juergenpabel/HAL9000/enclosure/services/dashboard/resources/images/ATM.jpg

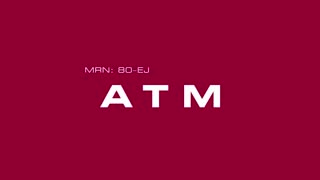
enclosure/services/dashboard/resources/images/ATM.jpg
