juergenpabel/HAL9000/enclosure/services/dashboard/resources/images/CNT.jpg

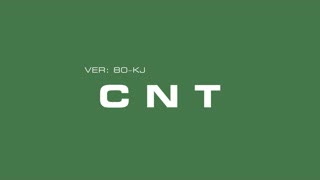
enclosure/services/dashboard/resources/images/CNT.jpg
