juergenpabel/HAL9000/enclosure/services/dashboard/resources/images/FLX.jpg

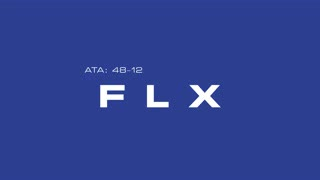
enclosure/services/dashboard/resources/images/FLX.jpg
