juergenpabel/HAL9000/enclosure/services/frontend/resources/images/animations/hal9000/fade-in/01.jpg

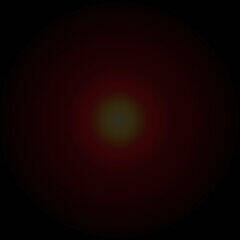
enclosure/services/frontend/resources/images/animations/hal9000/fade-in/01.jpg
