juergenpabel/HAL9000/enclosure/services/frontend/resources/images/animations/hal9000/fade-in/02.jpg

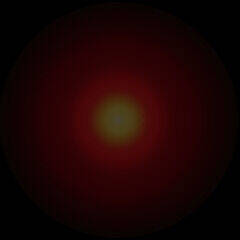
enclosure/services/frontend/resources/images/animations/hal9000/fade-in/02.jpg
