juergenpabel/HAL9000/enclosure/services/frontend/resources/images/animations/hal9000/fade-out/08.jpg

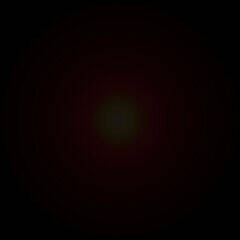
enclosure/services/frontend/resources/images/animations/hal9000/fade-out/08.jpg
