juergenpabel/HAL9000/enclosure/services/frontend/resources/images/animations/shutdown/power-off/fade-in/00.jpg

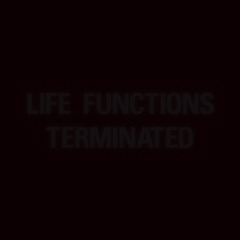
enclosure/services/frontend/resources/images/animations/shutdown/power-off/fade-in/00.jpg
