juergenpabel/HAL9000/enclosure/services/frontend/resources/images/animations/shutdown/power-off/fade-out/03.jpg

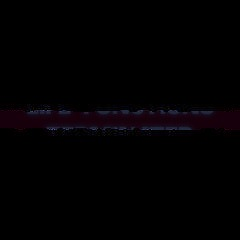
enclosure/services/frontend/resources/images/animations/shutdown/power-off/fade-out/03.jpg
