juergenpabel/HAL9000/enclosure/services/frontend/resources/images/animations/shutdown/power-off/loop/01.jpg

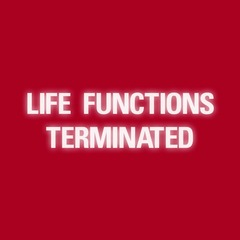
enclosure/services/frontend/resources/images/animations/shutdown/power-off/loop/01.jpg
