juergenpabel/HAL9000/enclosure/services/frontend/resources/images/animations/shutdown/system-stopping/02.jpg

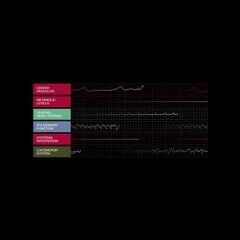
enclosure/services/frontend/resources/images/animations/shutdown/system-stopping/02.jpg
