juergenpabel/HAL9000/enclosure/services/frontend/resources/images/animations/shutdown/system-stopping/66.jpg

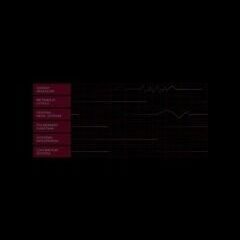
enclosure/services/frontend/resources/images/animations/shutdown/system-stopping/66.jpg
