juergenpabel/HAL9000/enclosure/services/frontend/resources/images/animations/startup/power-on/02.jpg

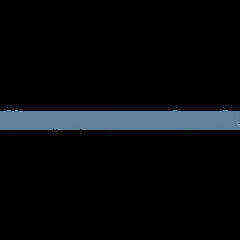
enclosure/services/frontend/resources/images/animations/startup/power-on/02.jpg
