juergenpabel/HAL9000/enclosure/services/frontend/resources/images/animations/startup/power-on/11.jpg

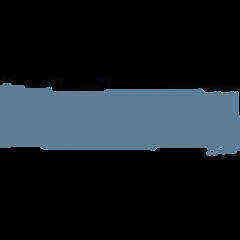
enclosure/services/frontend/resources/images/animations/startup/power-on/11.jpg
