juergenpabel/HAL9000/enclosure/services/frontend/resources/images/animations/startup/system-configuring/fade-in/07.jpg

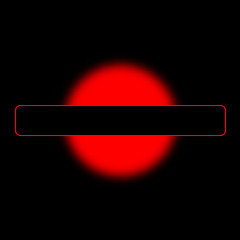
enclosure/services/frontend/resources/images/animations/startup/system-configuring/fade-in/07.jpg
