juergenpabel/HAL9000/enclosure/services/frontend/resources/images/animations/startup/system-configuring/loop/01.jpg

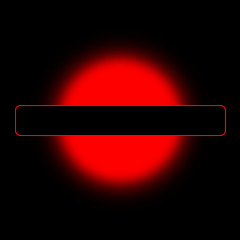
enclosure/services/frontend/resources/images/animations/startup/system-configuring/loop/01.jpg
