juergenpabel/HAL9000/enclosure/services/frontend/resources/images/animations/startup/system-starting/02.jpg

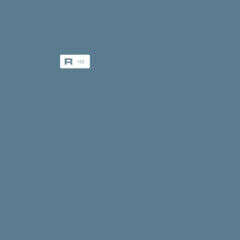
enclosure/services/frontend/resources/images/animations/startup/system-starting/02.jpg
