juergenpabel/HAL9000/enclosure/services/frontend/resources/images/animations/startup/system-starting/06.jpg

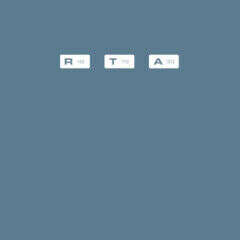
enclosure/services/frontend/resources/images/animations/startup/system-starting/06.jpg
