juergenpabel/HAL9000/src/client/html/images/hal9000.png

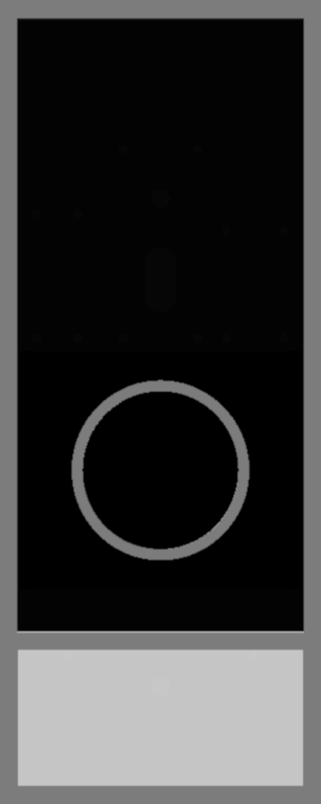
src/client/html/images/hal9000.png
