juergenpabel/HAL9000/resources/openscad/hal9000-part_display-cover.scad

include <hal9000.scad>

conf_display = "m5core2"; //"roundypi"

hal9000_component_display_cover();
