juergenpabel/HAL9000/resources/openscad/hal9000-part_display-frame-bottom.scad

include <hal9000.scad>

hal9000_component_display_frame_bottom();
