juergenpabel/HAL9000/resources/openscad/hal9000-part_display-ring.scad

include <hal9000.scad>

hal9000_component_display_ring();
