juergenpabel/HAL9000/resources/openscad/hal9000-part_enclosure-bottom.scad

include <hal9000.scad>

hal9000_enclosure_bottom();
