juergenpabel/HAL9000/resources/openscad/hal9000-part_enclosure-panel_addons.scad

include <hal9000.scad>

conf_panel_rfid = true;
conf_panel_motion = true;

rotate([+00.0,+00.0,+90.0]) hal9000_enclosure_panel_addons();
