juergenpabel/HAL9000/resources/openscad/hal9000-part_enclosure-top.scad

include <hal9000.scad>

rotate([+00.0,+00.0,180.0]) hal9000_enclosure_top();
