juergenpabel/HAL9000/enclosure/services/frontend/package/hal9000/frontend/arduino/hal9000.py

from os.path import exists as os_path_exists
from time import monotonic as time_monotonic
from json import loads as json_loads, dumps as json_dumps
from configparser import ConfigParser as configparser_ConfigParser, \
                         ParsingError as configparser_ParsingError
from serial import Serial as serial_Serial, EIGHTBITS as serial_EIGHTBITS, \
                   PARITY_NONE as serial_PARITY_NONE, STOPBITS_ONE as serial_STOPBITS_ONE, \
                   SerialException as serial_SerialException
from asyncio import sleep as asyncio_sleep, create_task as asyncio_create_task
from usb import busses as usb_busses

from fastapi import FastAPI as fastapi_FastAPI

import logging
from hal9000.frontend import Frontend, RUNLEVEL, STATUS


class HAL9000(Frontend):

	def __init__(self, app: fastapi_FastAPI) -> None:
		super().__init__('arduino')
		self.serial = None
		self.serial_chunk = bytearray(b'')


	async def configure(self, configuration: configparser_ConfigParser) -> bool:
		arduino_device   = configuration.getstring('frontend:arduino', 'device',   fallback=None)
		arduino_baudrate = configuration.getint   ('frontend:arduino', 'baudrate', fallback=115200)
		arduino_timeout  = configuration.getfloat ('frontend:arduino', 'timeout',  fallback=0.01)
		if arduino_device is None:
			self.logger.info(f"[frontend:arduino] no device configured (section 'frontend:arduino', option 'device' in frontend.ini)")
			return None
		if os_path_exists(arduino_device) is False:
			self.logger.error(f"[frontend:arduino] configured device '{arduino_device}' does not exist")
			return None
		while self.serial is None:
			try:
				arduino_name = None
				for bus in usb_busses():
					for device in bus.devices:
						arduino_name = configuration.get('arduino:devices', f'{device.idVendor:04x}:{device.idProduct:04x}', fallback=arduino_name)
				if arduino_name is None:
					error = 'no error details provided' #TODO
					self.logger.critical(f"[frontend:arduino] no (known/configured) arduino found via USB: {error}")
					self.serial.close()
					self.serial = None
					return False
				self.logger.info(f"[frontend:arduino] identified /dev/ttyHAL9000 as '{arduino_name}'")
				self.serial = serial_Serial(port=arduino_device, timeout=arduino_timeout, baudrate=arduino_baudrate, \
				                            bytesize=serial_EIGHTBITS, parity=serial_PARITY_NONE, stopbits=serial_STOPBITS_ONE)
				self.logger.debug(f"[frontend:arduino] opened '{arduino_device}'")
				arduino_runlevel = await self.serial_await_runlevel_change('starting')
				if arduino_runlevel == 'configuring':
					self.logger.debug(f"[frontend:arduino] arduino status is now 'configuring'")
					i2c_bus = configuration.getint(f'arduino:{arduino_name}', 'i2c-bus', fallback=None)
					i2c_addr = configuration.getint(f'arduino:{arduino_name}', 'i2c-address', fallback=None)
					if i2c_bus is None or i2c_addr is None:
#TODO
						return False
					await self.serial_writeline(json_dumps(['peripherals/mcp23X17', {'init': {'i2c-bus': i2c_bus, 'i2c-address': i2c_addr}}]))
					await asyncio_sleep(0.5)
					if f'arduino:{arduino_name}:mcp23X17' in configuration.sections(): #TODO
						for key in configuration.options(f'arduino:{arduino_name}:mcp23X17'):
							if ':' in key:
								input_type, input_name = key.split(':', 1)
								input_list = configuration.getlist(f'arduino:{arduino_name}:mcp23X17', key)
								mcp23X17_data = {'config': {'device': {'type': input_type, 'name': input_name, 'inputs': []}}}
								for input in input_list:
									label, pin = input.split(':', 1)
									if input_type == 'button' or input_type == 'switch':
										mcp23X17_data['config']['device']['inputs'].append({'pin': pin, 'label': label, 'pullup': 'true'})
										mcp23X17_data['config']['device']['events'] = {'low': 'on', 'high': 'off'}
									elif input_type == 'rotary':
										mcp23X17_data['config']['device']['inputs'].append({'pin': pin, 'label': label})
									else:
										raise configparser_ParsingError(f"Unknown prefix '{input_type}' in '{arduino_name}:mcp23X17')")
								await self.serial_writeline(json_dumps(['peripherals/mcp23X17', mcp23X17_data]))
								await asyncio_sleep(0.5)
							else:
								raise configparser_ParsingError(f"Unsupported item '{key}' in section '{arduino_name}:mcp23X17')")
						await self.serial_writeline(json_dumps(['peripherals/mcp23X17', {'start': True}]))
						await asyncio_sleep(0.5)
					self.logger.debug(f"[frontend:arduino] '{arduino_device}' is now configured")
					await self.serial_writeline(json_dumps(['system/runlevel', 'running']))
					arduino_runlevel = await self.serial_await_runlevel_change('configuring')
				if arduino_runlevel == 'panicing':
					error = 'no error details provided' #TODO
					self.logger.critical(f"[frontend:arduino] arduino status is now 'panicing': {error}")
					self.serial.close()
					self.serial = None
					return False
				self.logger.debug(f"[frontend:arduino] arduino status is now 'running'")
			except (configparser_ParsingError, serial_SerialException) as e:
				self.logger.error(f"[frontend:arduino] {e}")
				if self.serial is not None:
					self.serial.close()
					self.serial = None
				return False

		return True


	async def start(self) -> None:
		await super().start()
		self.tasks['host2device'] = asyncio_create_task(self.task_host2device())
		self.tasks['device2host'] = asyncio_create_task(self.task_device2host())


	async def serial_readline(self, timeout: float = 0) -> None:
		if timeout > 0:
			timeout += time_monotonic()
		chunk = b''
		while b'\n' not in chunk:
			if timeout > 0 and time_monotonic() > timeout:
				return None
			if self.serial is None or self.serial.is_open is False:
				return None
			chunk = self.serial.readline()
			if len(chunk) > 0:
				self.serial_chunk.extend(chunk)
			else:
				await asyncio_sleep(0.001)
		line = None
		while line is None:
			try:
				line = self.serial_chunk.decode('utf-8').strip('\n')
			except UnicodeDecodeError as e:
				invalid_chunk = bytearray(b'')
				if e.end >= 0 and e.end < len(self.serial_chunk):
					invalid_chunk = self.serial_chunk[0:e.end]
					self.serial_chunk = self.serial_chunk[e.end:-1]
				else:
					invalid_chunk = self.serial_chunk
					line = ''
				self.logger.warning(f"[frontend:arduino] dropping part of received line due to utf-8 decoding issue: {invalid_chunk}")
		self.logger.log(Frontend.LOG_LEVEL_TRACE, f"[frontend:arduino] D->H: {line}")
		self.serial_chunk = bytearray(b'')
		if isinstance(line, str) is True and (len(line) < 8 or line[0] != '[' or line[-1] != ']'):
			self.logger.warning(f"[frontend:arduino] skipping over non-webserial message (probably an arduino error message): {line}")
			line = None
		return line


	async def serial_writeline(self, line: str) -> None:
		if self.serial is None or self.serial.is_open is not True:
			self.logger.error(f"[frontend:arduino] serial_writeline('{line}') failed as serial connection is not established")
			return
		self.logger.log(Frontend.LOG_LEVEL_TRACE, f"[frontend:arduino] H->D: {line}")
		self.serial.write(f'{line}\n'.encode('utf-8'))


	async def serial_await_runlevel_change(self, runlevel: str, timeout: float = 1.0) -> str:
		await self.serial_writeline(json_dumps(['system/runlevel', '']))
		line = None
		response = ['system/runlevel', runlevel]
		while response[0] != 'system/runlevel' or response[1] == runlevel:
			line = None
			while line is None:
				line = await self.serial_readline(timeout=1.0)
			try:
				response = json_loads(line)
				if response[0] == 'ping':
					await self.serial_writeline(json_dumps(['pong', '']))
			except Exception as e:
				self.logger.info(f"[frontend:arduino] ignoring line with unexpected format: {line}")
		return response[1]


	async def task_host2device(self) -> None:
		self.logger.debug(f"[frontend:arduino] starting host2device-listener")
		while os_path_exists(self.serial.port) and self.tasks['host2device'].cancelled() is False:
			if self.serial.is_open is False:
				self.serial.open()
				await asyncio_sleep(1)
			try:
				while self.serial.is_open is True and self.tasks['host2device'].cancelled() is False:
					self.status = STATUS.ONLINE
					command = await self.commands.get()
					if isinstance(command, dict) and 'topic' in command and 'payload' in command:
						if command['topic'] != 'pong':
							self.logger.debug(f"[frontend:arduino] host2device sends message: {command}")
						command = json_dumps([command['topic'], command['payload']])
						await self.serial_writeline(command)
				self.logger.warning(f"[frontend:arduino] serial device '{self.serial.port}' (unexpectedly) closed")
			except Exception as e:
				self.logger.error(f"[frontend:arduino] exception in task_host2device(): {e}")
			self.status = STATUS.OFFLINE
		self.logger.error(f"[frontend:arduino] exiting host2device-listener ('arduino' frontend becomes non-functional)")
		del self.tasks['host2device']


	async def task_device2host(self) -> None:
		self.logger.debug(f"[frontend:arduino] starting device2host-listener")
		while os_path_exists(self.serial.port) and self.tasks['device2host'].cancelled() is False:
			if self.serial.is_open is False:
				self.serial.open()
				await asyncio_sleep(1)
			try:
				while self.serial.is_open is True and self.tasks['device2host'].cancelled() is False:
					if self.status != STATUS.ONLINE:
						self.status = STATUS.ONLINE
						self.commands.put_nowait(None) # to wake up task_host2device()
					line = await self.serial_readline()
					try:
						event = json_loads(line)
						if isinstance(event, list) and len(event) == 2:
							if event[0] == 'ping':
								self.commands.put_nowait({'topic': 'pong', 'payload': ''})
								event[0] = ''
							else:
								self.logger.debug(f"[frontend:arduino] device2host reads message: " \
								                  f"{json_dumps({'topic': event[0], 'payload': event[1]})}")
							if event[0].startswith('syslog/'):
								log_level = event[0][7:].upper()
								if hasattr(logging, log_level) is True:
									log_level = getattr(logging, log_level)
									self.logger.log(log_level, f"[frontend:arduino] {event[0]}: {json_dumps(event[1])}")
							if isinstance(event[1], dict) is True:
								if 'origin' not in event[1]:
									event[1]['origin'] = 'frontend:arduino'
							if event[0] != '':
								self.events.put_nowait({'topic': event[0], 'payload': event[1]})
						else:
							self.logger.warning(f"[frontend:arduino] unexpected (but valid) JSON structure received: {line}")
					except Exception as e:
						self.logger.error(f"[frontend:arduino] {e}")
					await asyncio_sleep(0.01)
				self.logger.warning(f"[frontend:arduino] serial device '{self.serial.port}' (unexpectedly) closed")
			except Exception as e:
				self.logger.error(f"[frontend:arduino] exception in task_device2host(): {e}")
			self.status = STATUS.OFFLINE
		self.logger.error(f"[frontend:arduino] exiting device2host-listener ('arduino' frontend becomes non-functional)")
		del self.tasks['device2host']
		self.tasks['host2device'].cancel()
		await self.commands.put(None) # to wake up task_host2device()
