juergenpabel/HAL9000/enclosure/firmware/arduino/src/device/board/board.h

#ifndef __DEVICE_BOARD_BOARD_H__
#define __DEVICE_BOARD_BOARD_H__

#include <etl/string.h>
#include <ArduinoJson.h>


class AbstractBoard {
	protected:
		etl::string<GLOBAL_KEY_SIZE> m_identifier;
	public:
		AbstractBoard(const etl::string<GLOBAL_KEY_SIZE>& identifier) { this->m_identifier = identifier; };
		const etl::string<GLOBAL_KEY_SIZE>& getIdentifier() { return this->m_identifier; };

		virtual bool start();
		virtual bool configure(const JsonVariant& configuration) = 0;
		virtual void reset();
		virtual void halt();

		virtual bool isDisplay(bool on) = 0;
		virtual void displayOn() = 0;
		virtual void displayOff() = 0;
};

#endif
