juergenpabel/HAL9000/enclosure/firmware/arduino/src/device/board/m5stack-core2.h

#ifndef __DEVICE_BOARD_M5CORE2_H__
#define __DEVICE_BOARD_M5CORE2_H__

#ifdef ARDUINO_M5STACK_Core2

#define XPOWERS_CHIP_AXP2101
#include <XPowersLib.h>

#include "device/board/board.h"


class Board : public AbstractBoard {
	private:
		XPowersAXP2101 m_PMU;
	public:
		Board();
		virtual bool start();
		virtual bool configure(const JsonVariant& configuration);
		virtual void reset();
		virtual void halt();

		virtual bool isDisplay(bool status);
		virtual void displayOn();
                virtual void displayOff();
};

#endif

#endif
