juergenpabel/HAL9000/enclosure/firmware/arduino/src/device/board/sbcomponents-roundypi.cpp

#ifdef ARDUINO_SBCOMPONENTS_ROUNDYPI

#include <Arduino.h>
#include <TimeLib.h>

#include "device/board/sbcomponents-roundypi.h"
#include "globals.h"


Board::Board()
      :AbstractBoard("roundypi")
      , displayStatus(true) {
}


bool Board::start() {
	if(AbstractBoard::start() == false) {
		return false;
	}
	if(TFT_BL >= 0) {
		pinMode(TFT_BL, OUTPUT);
	}
	this->displayOn();
	return true;
}


bool Board::configure(const JsonVariant& configuration) {
	return g_device_microcontroller.configure(configuration);
}


void Board::reset() {
	AbstractBoard::reset();
}


void Board::halt() {
	this->displayOff();
	AbstractBoard::halt();
}


bool Board::isDisplay(bool status) {
	return this->displayStatus == status;
}


void Board::displayOn() {
	if(TFT_BL >= 0) {
		digitalWrite(TFT_BL, HIGH);
                this->displayStatus = true;
	}
}


void Board::displayOff() {
	if(TFT_BL >= 0) {
		digitalWrite(TFT_BL, LOW);
                this->displayStatus = false;
	}
}

#endif
