juergenpabel/HAL9000/enclosure/firmware/arduino/src/system/environment.h

#ifndef __SYSTEM_ENVIRONMENT_H__
#define __SYSTEM_ENVIRONMENT_H__

#include <etl/string.h>
#include <etl/map.h>
#include <ArduinoJson.h>


typedef etl::map<etl::string<GLOBAL_KEY_SIZE>, etl::string<GLOBAL_VALUE_SIZE>, APPLICATION_ENVIRONMENT_MAX> EnvironmentMap;
class Application;

class Environment : public EnvironmentMap {
	protected:
		Environment() : EnvironmentMap() {};

	friend class Application;
};


class EnvironmentWriter {
	private:
		Application& application;
		etl::string<GLOBAL_KEY_SIZE> key;
	protected:
		EnvironmentWriter(Application& application, const etl::string<GLOBAL_KEY_SIZE>& key);
	public:
		size_t write(uint8_t c);
		size_t write(const uint8_t *buffer, size_t length);

	friend class Application;
};

#endif
