juergenpabel/HAL9000/enclosure/firmware/arduino/src/device/board/roundypi.cpp

#ifdef ARDUINO_ROUNDYPI

#include <Arduino.h>
#include <TimeLib.h>

#include "device/board/roundypi.h"
#include "globals.h"


Board::Board()
      :AbstractBoard("roundypi") {
}


void Board::start(bool& host_booting) {
	AbstractBoard::start(host_booting);
	if(TFT_BL >= 0) {
		pinMode(TFT_BL, OUTPUT);
	}
	this->displayOn();
}


bool Board::configure(const JsonVariant& configuration) {
	return g_device_microcontroller.configure(configuration);
}


void Board::reset(bool host_rebooting) {
	AbstractBoard::reset(host_rebooting);
}


void Board::halt() {
	this->displayOff();
	AbstractBoard::halt();
}


void Board::displayOn() {
	if(TFT_BL >= 0) {
		digitalWrite(TFT_BL, HIGH);
	}
}


void Board::displayOff() {
	if(TFT_BL >= 0) {
		digitalWrite(TFT_BL, LOW);
	}
}

#endif
