juergenpabel/HAL9000/enclosure/src/firmware/display/roundypi/src/globals.h

#include "defines.h"
#include <TFT_eSPI.h>
#include <SimpleWebSerial.h>


extern TFT_eSPI        g_tft;
extern SimpleWebSerial g_webserial;

extern sequence_t* g_current_sequence;
extern sequence_t  g_sequences_queue[];
