juergenpabel/HAL9000/enclosure/firmware/arduino/src/util/jpeg.h

#include <etl/string.h>
#include <JPEGDEC.h>

void util_jpeg_decode565_littlefs(const etl::string<GLOBAL_FILENAME_SIZE>& filename, uint16_t* image565_data, uint32_t image565_size, JPEG_DRAW_CALLBACK* image_func = nullptr);
