juergenpabel/HAL9000/enclosure/firmware/arduino/src/gui/webserial.h

#include <ArduinoJson.h>

void on_gui_overlay(const etl::string<GLOBAL_KEY_SIZE>& command, const JsonVariant& data);
void on_gui_screen(const etl::string<GLOBAL_KEY_SIZE>& command, const JsonVariant& data);
