juergenpabel/HAL9000/enclosure/src/firmware/roundypi/src/gui/overlay.cpp

#include "globals.h"

#include <string.h>
#include <TimeLib.h>
#include <LittleFS.h>
#include <SimpleWebSerial.h>
#include "screen.h"
#include "overlay.h"


static overlay_update_func g_current_update_func = overlay_update_noop;

overlay_update_func overlay_update(overlay_update_func new_update_func) {
	overlay_update_func previous_update_func = NULL;

	if(new_update_func != NULL) {
		previous_update_func = g_current_update_func;
		g_current_update_func = new_update_func;
		screen_update(screen_update_noop, true);
	}
	g_current_update_func();
	return previous_update_func;
}


void overlay_update_noop() {
	g_tft_overlay.fillSprite(TFT_TRANSPARENT);
}


void overlay_update_volume() {
	g_tft_overlay.fillSprite(TFT_TRANSPARENT);
	g_tft_overlay.setTextColor(TFT_WHITE, TFT_TRANSPARENT);
	g_tft_overlay.drawString("Volume: " + g_settings["volume-current"], 80, 0);
}
